Vishal-Mutha/sra-board-hardware-design/documentation/assets/3d_sideview.png

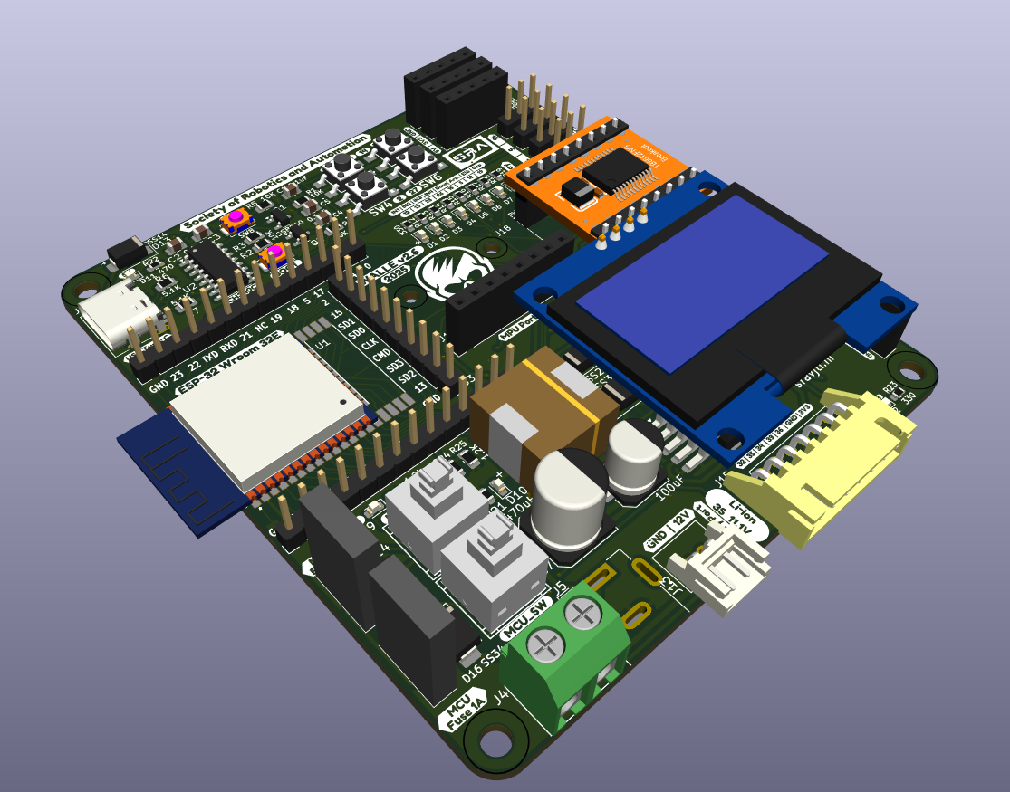
documentation/assets/3d_sideview.png
