Vishal-Mutha/sra-board-hardware-design/documentation/images/board_images/bottom_silk_layer.png

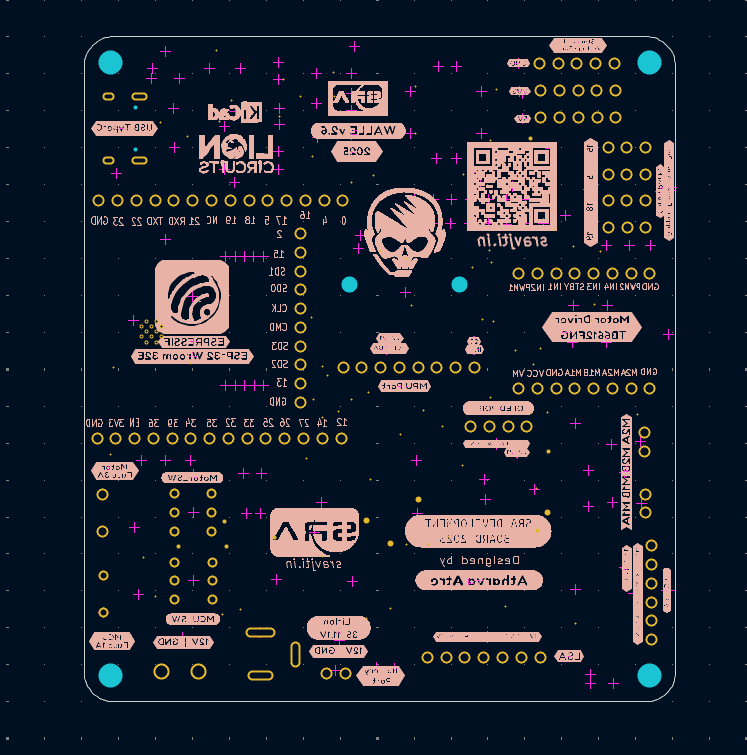
documentation/images/board_images/bottom_silk_layer.png
