Vishal-Mutha/sra-board-hardware-design/documentation/images/board_images/bottom_silkscreen.png

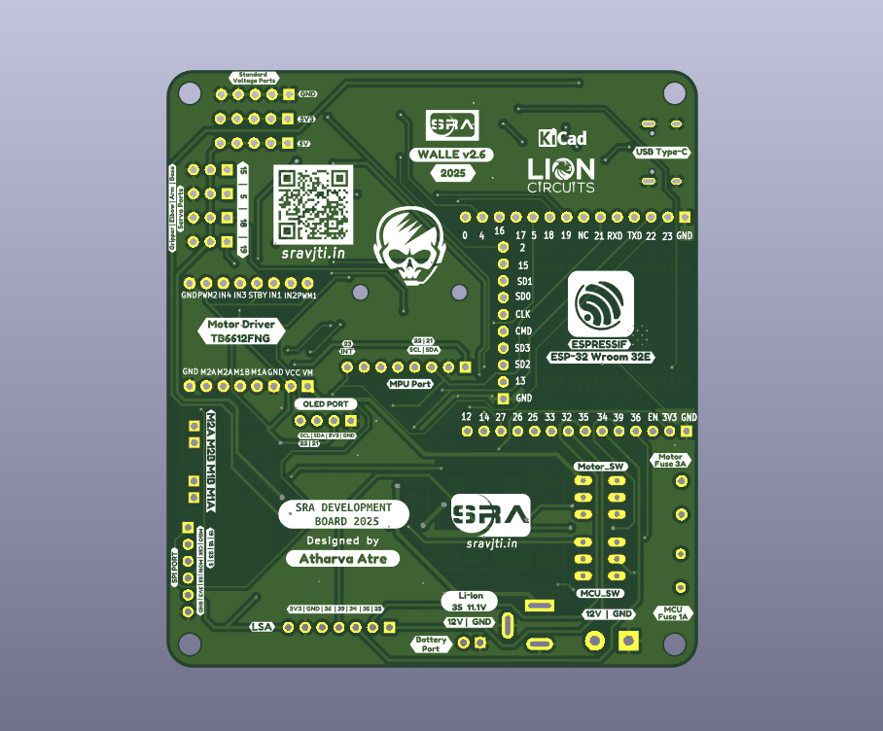
documentation/images/board_images/bottom_silkscreen.png
