Vishal-Mutha/sra-board-hardware-design/documentation/images/board_images/fcu.png

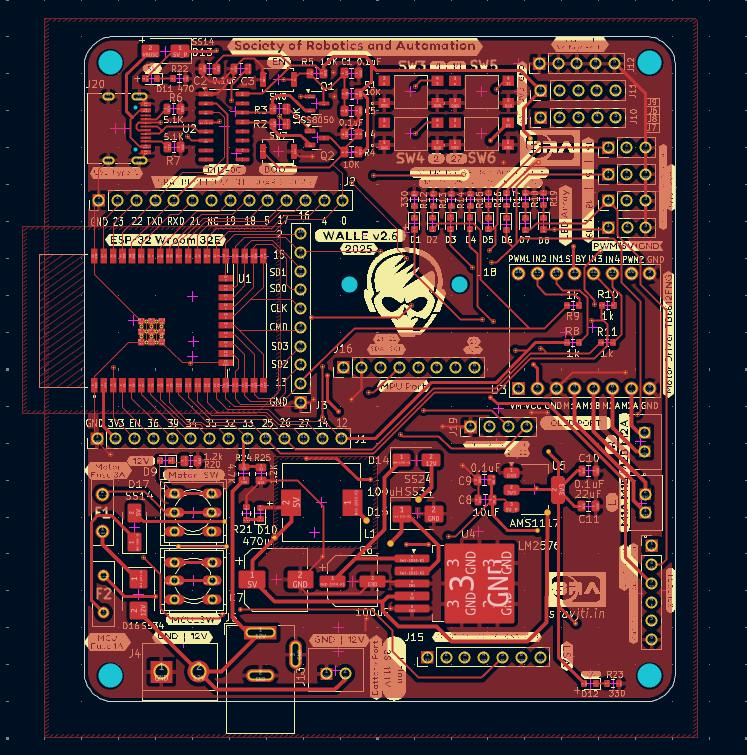
documentation/images/board_images/fcu.png
