Vishal-Mutha/sra-board-hardware-design/documentation/images/board_images/front_view_4.png

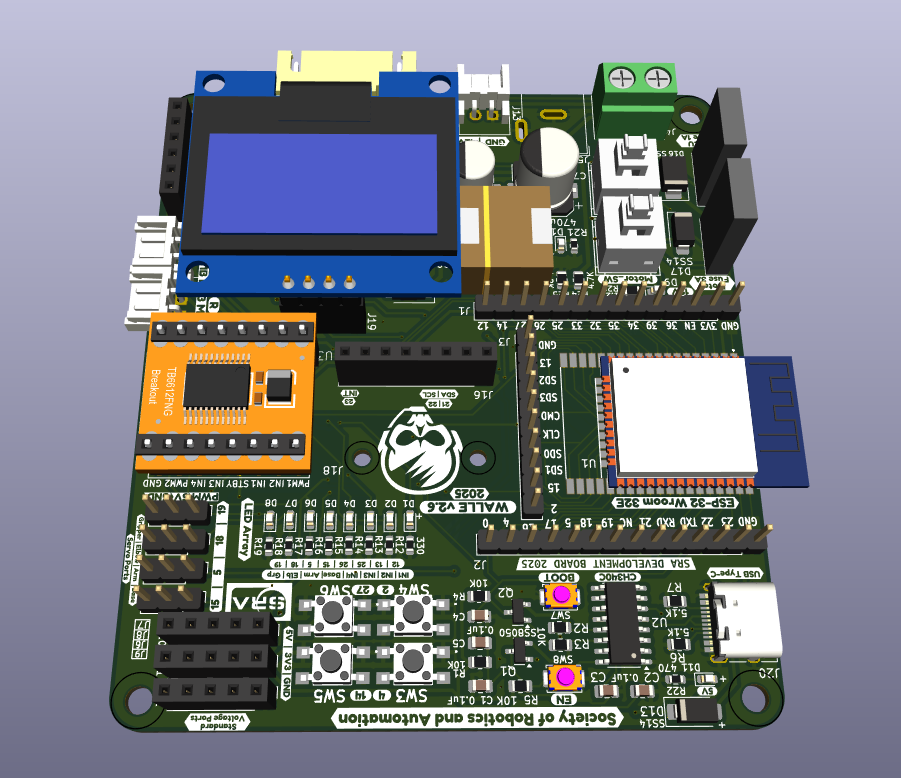
documentation/images/board_images/front_view_4.png
