Vishal-Mutha/sra-board-hardware-design/documentation/images/board_images/lable_view.png

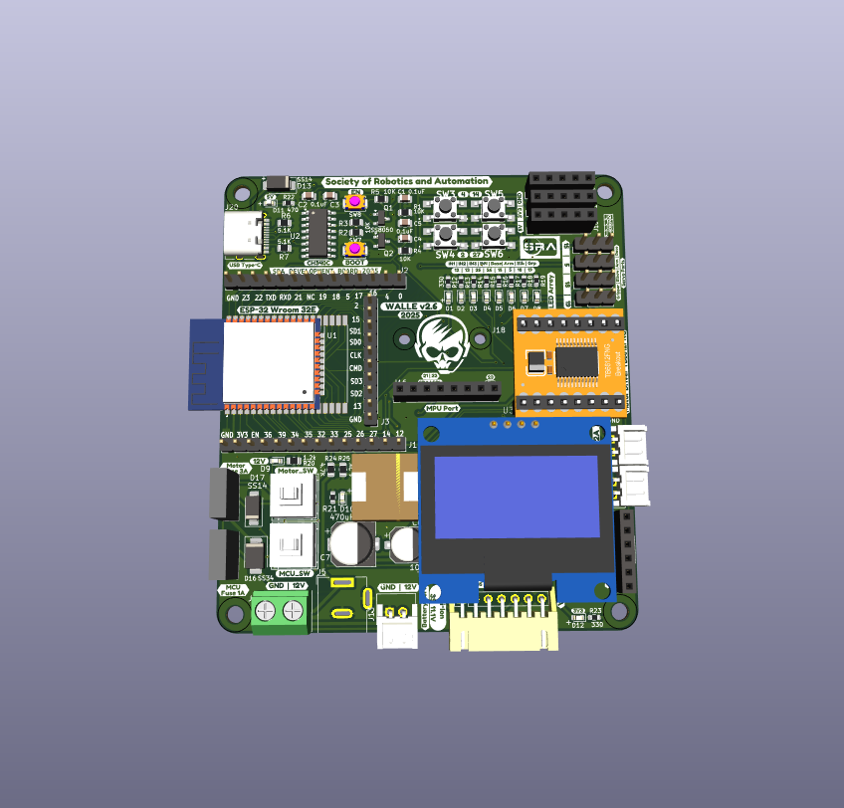
documentation/images/board_images/lable_view.png
