Vishal-Mutha/sra-board-hardware-design/documentation/images/board_images/routing_both.png

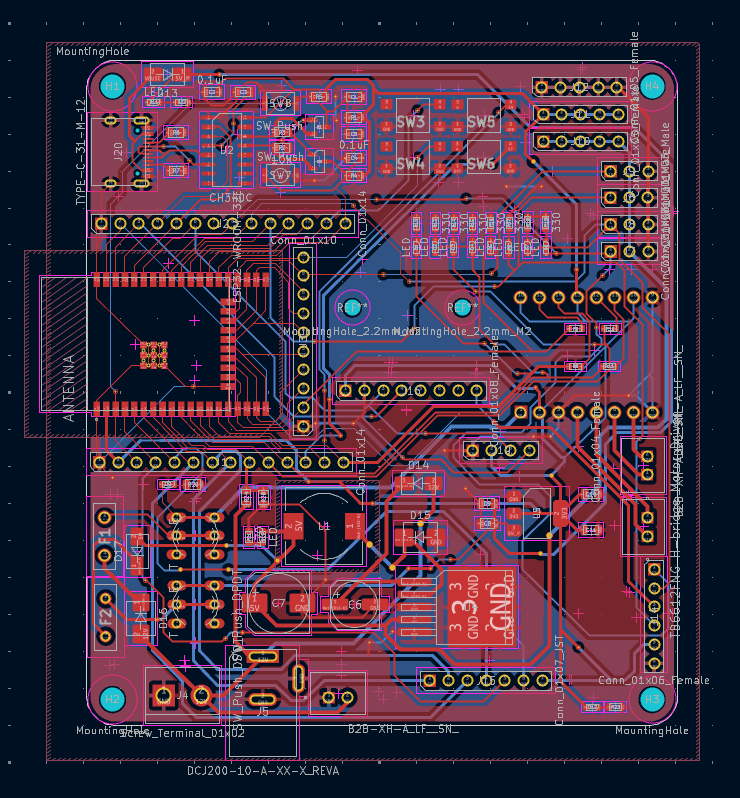
documentation/images/board_images/routing_both.png
