Vishal-Mutha/sra-board-hardware-design/documentation/images/board_images/routing_bottom.png

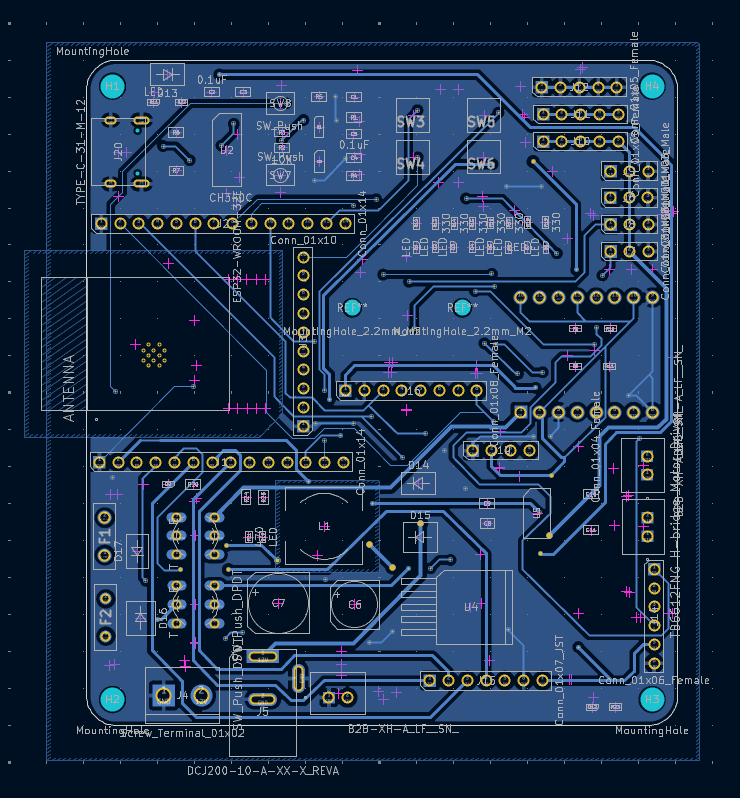
documentation/images/board_images/routing_bottom.png
