Vishal-Mutha/sra-board-hardware-design/documentation/images/board_images/routing_front.png

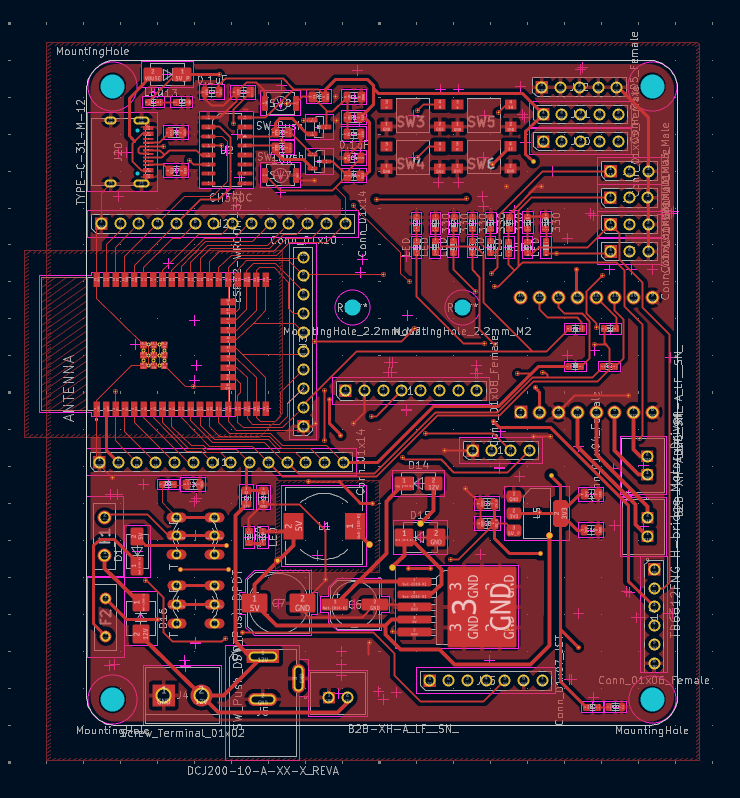
documentation/images/board_images/routing_front.png
