Vishal-Mutha/sra-board-hardware-design/sra_dev_board_2025/component_libraries/oled/ER-OLEDM013-1-SPI-I2C_3D Drawing.jpg

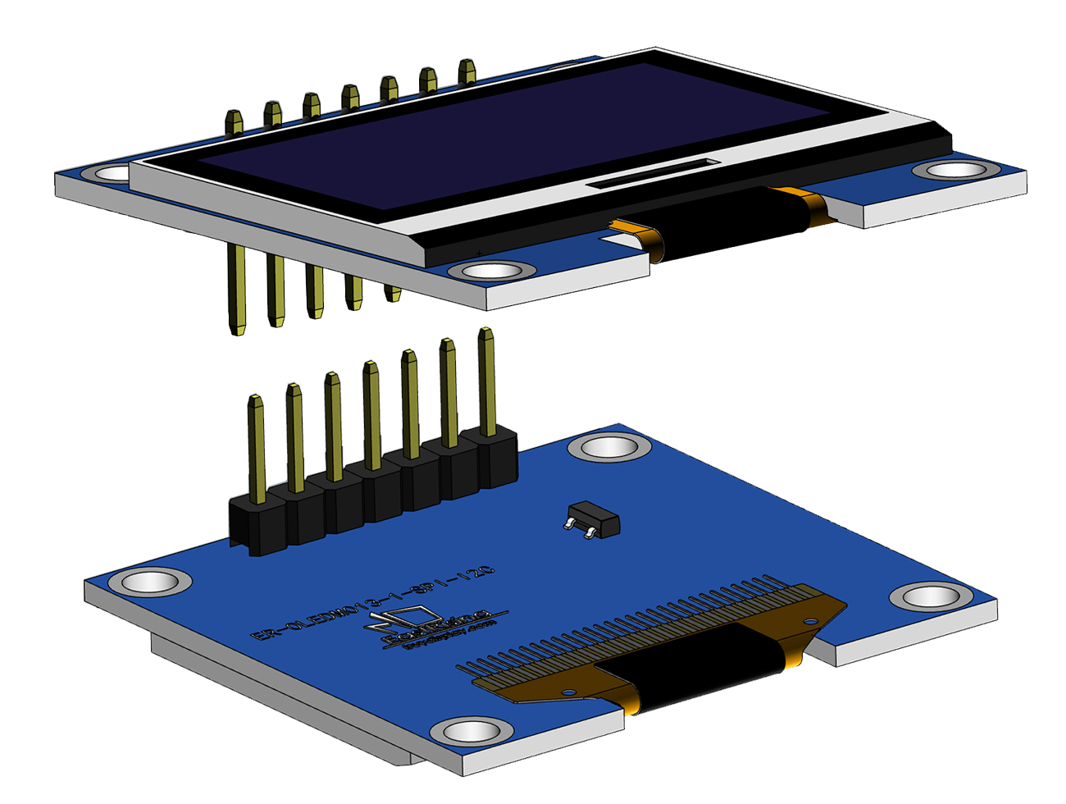
sra_dev_board_2025/component_libraries/oled/ER-OLEDM013-1-SPI-I2C_3D Drawing.jpg
