Vishal-Mutha/sra-board-hardware-design/sra_dev_board_2025/component_libraries/oled/PCB v8.png

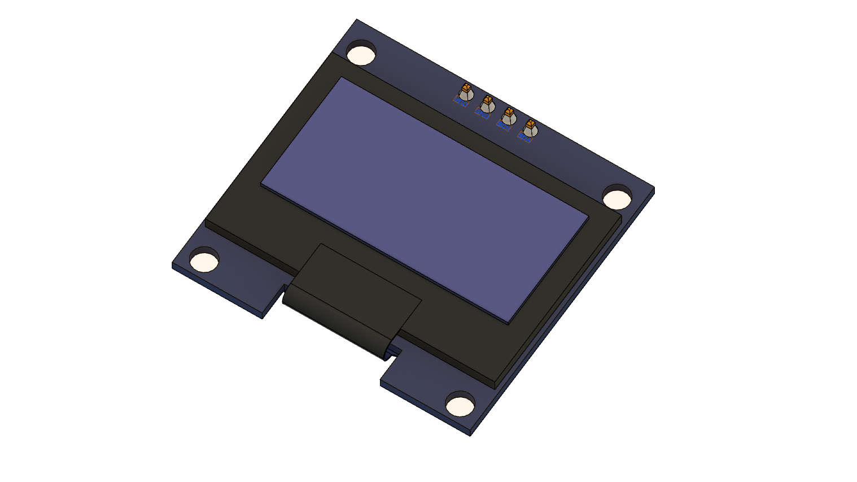
sra_dev_board_2025/component_libraries/oled/PCB v8.png
