Vishal-Mutha/sra-board-hardware-design/sra_dev_board_2025/component_libraries/oled/Serial SPI I2C Blue 1.3 inch Arduino,Raspberry Pi OLED Display 128x64.jpg

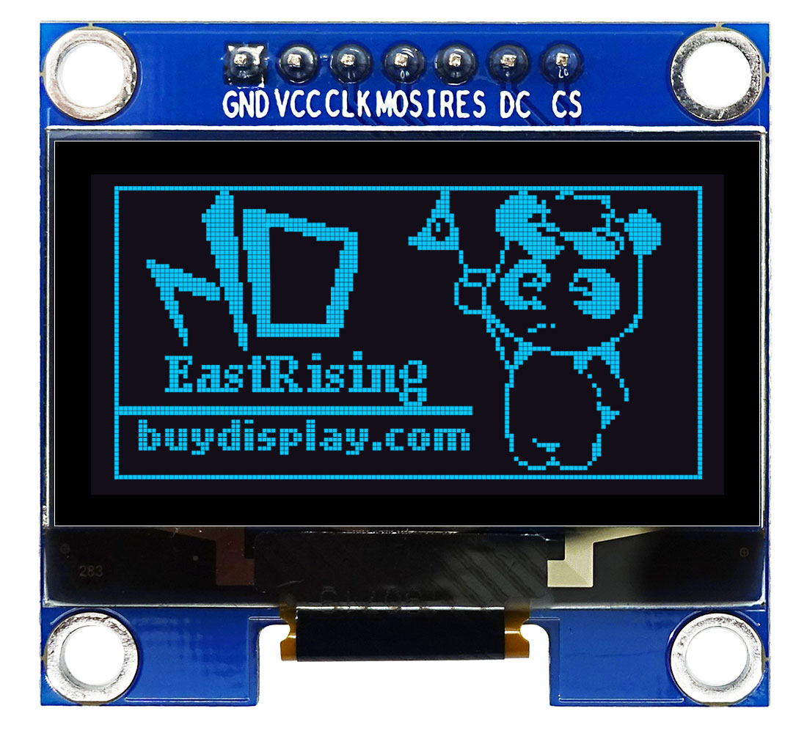
sra_dev_board_2025/component_libraries/oled/Serial SPI I2C Blue 1.3 inch Arduino,Raspberry Pi OLED Display 128x64.jpg
