Vishal-Mutha/sra-board-hardware-design/sra_dev_board_2025/component_libraries/switches/Esp-32 Switch/skrkaee010.stp

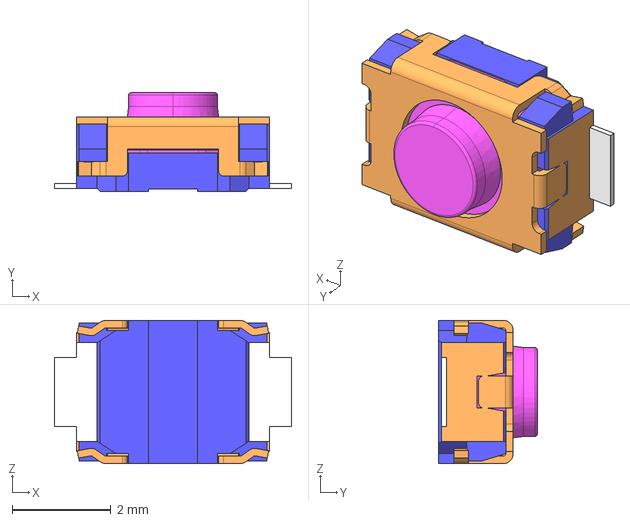
[picture p45: CAD file, 2025-04-24]
sra_dev_board_2025/component_libraries/switches/Esp-32 Switch/skrkaee010.stp
4.80 x 2.00 x 2.90 mm
