Vishal-Mutha/sra-board-hardware-design/sra_dev_board_2025/component_libraries/switches/tactile_smd/spst_tactile_sw_2x02_smd.stp

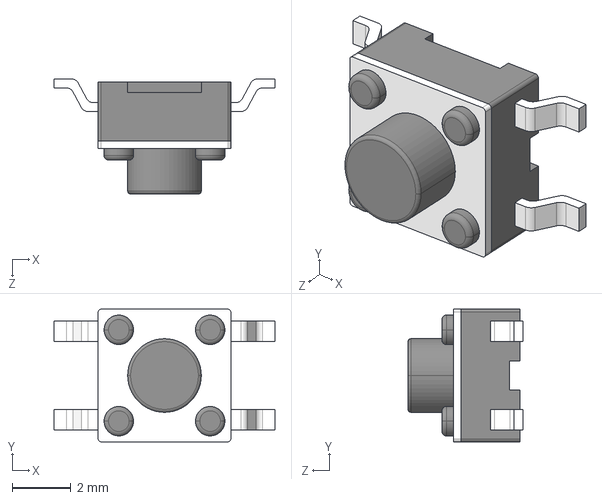
[picture p46: CAD file, 2025-04-24]
sra_dev_board_2025/component_libraries/switches/tactile_smd/spst_tactile_sw_2x02_smd.stp
7.50 x 4.50 x 3.90 mm
