Vishal-Mutha/sra-board-hardware-design/sra_dev_board_2025/component_libraries/terminal_block/12V_1x02_tht.step

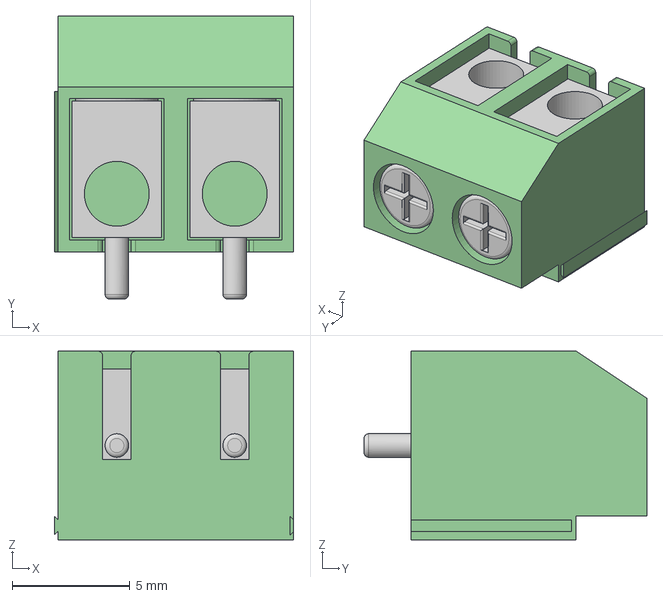
[picture p47: CAD file, 2025-04-24]
sra_dev_board_2025/component_libraries/terminal_block/12V_1x02_tht.step
10.2 x 12.0 x 8.00 mm
