Vishal-Mutha/sra-board-hardware-design/sra_dev_board_2025/component_libraries/inductor/CDRH104R_inductor_smd.stp

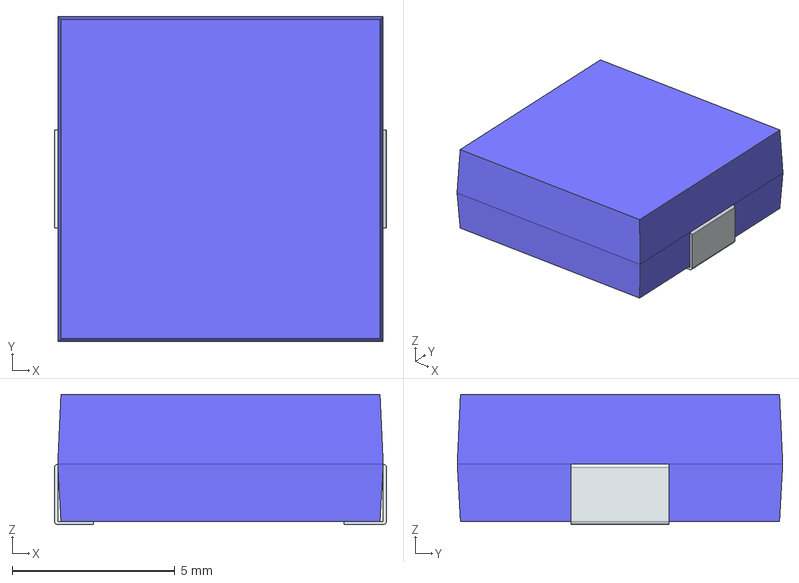
[picture p48: CAD file, 2025-04-24]
sra_dev_board_2025/component_libraries/inductor/CDRH104R_inductor_smd.stp
10.2 x 10.0 x 4.00 mm
FilletPin1
FilletPin2
